jamro/desk-hud/src/backend/distance_mock.js

const data = `77
69
60
57
54
50
55
61
64
68
73
77
76
77
61
77
61
61
61
77
77
60
63
77
77
76
60
77
62
61
62
62
74
61
76
77
73
61
61
72
79
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
75`.split("\n")


let i = 0

setInterval(() => {
  //if(Math.random() > 0.99) throw new Error('Some test error')
  if(data[i]) {
    //console.log(data[i])
    console.log(20)
  }
  i++
  i = i % data.length
}, 50)
